WellDone/MoMo-Firmware/pcb/calculations/spice/controller/current_limiter.asc

D1: schottky; 1N5817
D2: schottky; 1N5817
M1: pmos; irlml6402
Q1: pnp
R1: res; 1
R2: res; 10k
R3: res; 100k
V1: voltage; 4.0
V3: voltage; PULSE(0 4.75 1 0.01 0.01 2)
V4: voltage; PULSE(0 3.8 0.5 0.01 0.01 2)
Named nets: 0
.tran 2
.lib irlml6402.spi
