WellDone/MoMo-Firmware/pcb/calculations/spice/controller/reset_circuit.asc

C1: cap; 1µ
C2: cap; 1µ
M1: nmos; 2N7002P
R1: res; 100k
R2: res; 100K
R3: res; 510K
R4: res; 10K
V1: voltage; PULSE(0 2.8 0.02 1e-6 1e-6 119e-3 2)
V2: voltage; 4.2
Named nets: V_enable, 0, discharge
.lib 2N7002P_8_18_2010.lib
.tran 0.5
Hardware Reset Generation
MoMo Controller v4.1
November 23, 2014
This circuit should reliably generate a
~100 ms low going pulse on V_enable
that must remain below 0.6V for > 50ms,
even without continued high input.
