WellDone/MoMo-Firmware/momo_modules/multi_sensor_module/src/state.h

#ifndef __state_h__
#define __state_h__

#include <stdint.h>

typedef struct
{
	union
	{
		struct
		{
			uint8_t acquire_pulse : 1;
			uint8_t push_pending : 1;
			uint8_t push_disabled: 1;
			uint8_t reserved : 5;
		};

		uint8_t combined_state;
	};
} MultiSensorState;

#endif
