WellDone/MoMo-Firmware/momo_modules/pic12_executive/src/bus_defines.h

#ifndef __bus_defines_h__
#define __bus_defines_h__

//Offsets from mib_data to the three overlapping buffers that store
//the command packet, return status and return value.
#define kCommandOffset 0
#define kReturnStatusOffset 1
#define kReturnValueOffset 3

//Bus error codes that can be returned
#define kNoMIBError 				0
#define kUnsupportedCommand 		1
#define kWrongParameterType 		2
#define kParameterTooLong 			3
#define kChecksumError				4
#define kUnknownError 				6
#define kCallbackError 				7
#define kSlaveNotAvailable 			255

//Other Constants
#define kInvalidMIBIndex			255
#define kBusMaxMessageSize 			20

#endif
