WellDone/MoMo-Firmware/momo_modules/mainboard/src/momo/report_manager.c

#include "report_manager.h"
#include "scheduler.h"
#include "momo_config.h"
#include "sensor_event_log.h"
#include "report_comm_stream.h"
#include "utilities.h"
#include "uart.h"
#include "base64.h"
#include "bus_master.h"
#include "perf.h"
#include "system_log.h"
#include "report_log.h"
#include "log_definitions.h"
#include <stdlib.h>
#include <string.h>

#define EVENT_BUFFER_SIZE         1

#define CONFIG current_momo_state.report_config

//Report structure, 118 bytes total
typedef struct 
{ 
    //18 byte header
    uint8          report_version;         // = 3, must be positive
    uint8          transmit_sequence;      //   How many times have we tried to transmit a report
    uint32         momo_uuid;              //   The unique ID of this MoMo
    uint16         flags;                  //   Various flags determining how the data will be aggregated and other things

    uint32         timestamp;
    uint16         battery_voltage;        //2

    uint8          bulk_aggregates;        //  The aggregate functions to run on the entire span
    uint8          interval_aggregates;    //  The aggregate functions to run on each interval

    union
    {
      struct
      {
      uint8        interval_type:4;        //  0: second, 1: minute, 2: hour, 3: day
      uint8        interval_step:4;        //
      };

      uint8        interval_union;
    };

    uint8          interval_count;         //  Up to 256 'intervals' each aggregated individually
    
    // 100 bytes for data (50 two byte report values)
    uint16         data[NUM_BUCKETS];
} Report;

typedef struct 
{
  uint16 count;
  uint16 min;
  uint16 max;
  uint16 sum;
} agg_counters;

static Report         report;
static ScheduledTask  report_task;
char                  base64_report_buffer[BASE64_REPORT_MAX_LENGTH+1];
static sensor_event   event_buffer[EVENT_BUFFER_SIZE];

//TODO: Implement dynamic report routing based on an initial "registration" ping to the coordinator address
#define DEFAULT_WEB_ROUTE "https://strato.welldone.org/gateway/http"
#define DEFAULT_SMS_ROUTE "+14159928370"
// UK ALT +447903568420
#define DEFAULT_GPRS_APN "JTM2M"

extern unsigned int last_battery_voltage;

void report_manager_start()
{
  if ( get_momo_state_flag( kStateFlagReportingEnabled ) )
    start_report_scheduling();
}

void init_report_config()
{
  strcpy( CONFIG.route_primary, DEFAULT_WEB_ROUTE );
  strcpy( CONFIG.route_secondary, DEFAULT_SMS_ROUTE );
  strcpy( CONFIG.gprs_apn, DEFAULT_GPRS_APN );
  CONFIG.transmit_sequence         = 0;
  CONFIG.report_interval           = kEveryDay;
  CONFIG.report_flags              = kReportFlagDefault;
  CONFIG.bulk_aggregates           = kAggMin | kAggMax;
  CONFIG.interval_aggregates       = kAggCount | kAggMean;
  CONFIG.retry_limit               = 3;

  //Make sure we initialize this scheduled task.
  report_task.flags = 0;

  init_comm_stream();
}

void update_interval_headers( Report* header, AlarmRepeatTime interval )
{
  switch ( interval )
  {
    case kEvery10Seconds:
      header->interval_union = pack_report_interval(kReportIntervalSecond, 1);
      header->interval_count = 10;
      break;
    case kEveryMinute:
      header->interval_union = pack_report_interval(kReportIntervalSecond, 6);
      header->interval_count = 10;
      break;
    case kEvery10Minutes:
      header->interval_union = pack_report_interval(kReportIntervalMinute, 1);
      header->interval_count = 10;
      break;
    case kEveryHour:
      header->interval_union = pack_report_interval(kReportIntervalMinute, 6);
      header->interval_count = 10;
      break;
    case kEveryDay:
    default:
      header->interval_union = pack_report_interval(kReportIntervalHour, 1);
      header->interval_count = 24;
      break;
  }
}

uint32 create_time_delta( const Report* header )
{
  //FIXME: is 0 a valid option for the caller of this function?
  switch ( header->interval_type )
  {
    case kReportIntervalSecond:
      return header->interval_step * header->interval_count;
    case kReportIntervalMinute:
      return 60 * header->interval_step * header->interval_count;
    case kReportIntervalHour:
      return 3600L * header->interval_step * header->interval_count;
  }
  return 0;
}

//Set bit counting routine from
//https://graphics.stanford.edu/~seander/bithacks.html
static uint8 agg_size(uint8 agg_set)
{
  uint8 size;

  for (size=0; agg_set; ++size)
    agg_set &= agg_set-1;

  return size;
}

static void init_agg( agg_counters* agg )
{
  agg->count = 0;
  agg->min = MAX_UINT16;
  agg->max = 0;
  agg->sum = 0;
}
static void update_agg( agg_counters* agg, sensor_event* event )
{
  ++(agg->count);
  agg->sum += event->value;
  if ( event->value < agg->min )
    agg->min = event->value;
  if ( event->value > agg->max )
    agg->max = event->value;
}
static uint8 finish_agg( agg_counters* agg, uint8 agg_set, uint8 index)
{
  if ( agg_set & kAggCount )
    report.data[index++] = agg->count;
  if ( agg_set & kAggSum )
    report.data[index++] = agg->sum;
  if ( agg_set & kAggMean )
    report.data[index++] = (agg->count==0)? 0 : agg->sum / agg->count;
  if ( agg_set & kAggMin )
    report.data[index++] = agg->min;
  if ( agg_set & kAggMax )
    report.data[index++] = agg->max;

  return index;
}

bool construct_report()
{
  PROFILE_START(kConstructReport);
  agg_counters    bulk_agg;
  agg_counters    int_agg;
  uint8           i, c;
  uint8           sensor_id = 0, curr_interval = 0;
  uint8           interval_bucket = agg_size(CONFIG.bulk_aggregates);
  uint8           max_bucket = NUM_BUCKETS - agg_size(CONFIG.interval_aggregates);

  //Initialize the report header
  report.report_version = MOMO_REPORT_VERSION;
  report.transmit_sequence = CONFIG.transmit_sequence;
  report.momo_uuid = current_momo_state.uuid;
  report.flags = CONFIG.report_flags;
  report.battery_voltage = last_battery_voltage;
  report.timestamp = rtcc_get_timestamp();
  report.bulk_aggregates = CONFIG.bulk_aggregates;
  report.interval_aggregates = CONFIG.interval_aggregates;

  update_interval_headers(&report, CONFIG.report_interval);

  uint32 time_delta = create_time_delta(&report);
  uint32 time_step = time_delta / report.interval_count;

  init_agg(&bulk_agg);
  init_agg(&int_agg);

  //Zero out the report structure
  for (i=0; i<NUM_BUCKETS; ++i)
    report.data[i] = 0;

  do
  {
    PROFILE_START(kProcessEventCounter);
    c = read_sensor_events( event_buffer, EVENT_BUFFER_SIZE );
    for ( i = 0; i < c; ++i )
    {
      if ( sensor_id == 0 )
        sensor_id = event_buffer[i].module;
      else if ( sensor_id != event_buffer[i].module )
        continue; // TODO: Support multiple sensor streams

      if (CONFIG.bulk_aggregates != kAggNone)
        update_agg( &bulk_agg, &event_buffer[i] );

      if (CONFIG.interval_aggregates != kAggNone)
      {
        uint32 time_seconds;
        uint8  event_interval;
        TimeIntervalDirection delta;

        if (interval_bucket >= max_bucket)
          continue; //TODO: Extend to a second SMS

        //Check if the event is too old and drop it
        //TODO: extend the report start backwards to pick up the dropped events?
        time_seconds = rtcc_timestamp_difference(event_buffer[i].timestamp, report.timestamp, &delta);
        if (time_seconds >= time_delta)
          continue;

        //Check if this event is somehow in the future
        if (delta == kNegativeDelta)
        {
          requeue_sensor_events( c - i );
          c = 0;
          break;
        }

        event_interval = report.interval_count - time_seconds/time_step - 1; //time_seconds/time_step < report.interval_count since time_seconds < time_delta

        //Check if this event corresponds to a new interval, in which case zero out the intervening
        //intervals.
        while (curr_interval < event_interval)
        {
          interval_bucket = finish_agg(&int_agg, CONFIG.interval_aggregates, interval_bucket);
          init_agg(&int_agg);

          ++curr_interval;
        }

        update_agg(&int_agg, &event_buffer[i]);
      }
    }
    PROFILE_END(kProcessEventCounter);
  }
  while (c > 0);

  //Finish the last interval
  if (CONFIG.interval_aggregates != kAggNone && interval_bucket < max_bucket)
    interval_bucket = finish_agg(&int_agg, CONFIG.interval_aggregates, interval_bucket);

  if ( CONFIG.bulk_aggregates != kAggNone)
    finish_agg(&bulk_agg, CONFIG.bulk_aggregates, 0);

  PROFILE_START(kEncodeReportCounter);
  i = base64_encode((const BYTE*)&report, RAW_REPORT_MAX_LENGTH, base64_report_buffer, BASE64_REPORT_MAX_LENGTH);
  PROFILE_END(kEncodeReportCounter);
  base64_report_buffer[i] = '\0';

  report_log_write( (BYTE*)&report );
  save_momo_state();
  
  PROFILE_END(kConstructReport);
  return true;
}

void post_report( void* arg ) 
{
  report_stream_abandon();
  LOG_DEBUG(kConstructingReportNotice);
  if (!construct_report( CONFIG.report_interval ))
  {
    LOG_CRITICAL(kFailedToConstructReportError);
    return; //TODO: Recover
  }

  LOG_DEBUG(kReportConstructedNotice);
  report_stream_send( base64_report_buffer );
}

void start_report_scheduling() {
  LOG_DEBUG(kReportSchedulingStartedNotice);
  scheduler_schedule_task( post_report, CONFIG.report_interval, kScheduleForever, &report_task, NULL );
}
void stop_report_scheduling() {
  LOG_DEBUG(kReportSchedulingStoppedNotice);
  scheduler_remove_task( &report_task );
}
void set_report_scheduling_interval( AlarmRepeatTime interval ) {
  if ( interval >= kNumAlarmTimes )
    return;

  CONFIG.report_interval = interval;
  if ( BIT_TEST(report_task.flags, kBeingScheduledBit) )
    scheduler_schedule_task( post_report, CONFIG.report_interval, kScheduleForever, &report_task, NULL );
  
  save_momo_state();
}
void update_report_route( uint8 index, uint8 start, const char* route, uint8 len )
{
  if ( index > 1 || start+len >= ROUTE_MAX_LENGTH )
    return;

  char* target = (index == 0)? CONFIG.route_primary : CONFIG.route_secondary;
  memcpy( target+start, route, len );
  target[start+len] = '\0';
  save_momo_state();
}

void set_gprs_apn( const char* apn, uint8 len )
{
  if ( len + 1 > sizeof(CONFIG.gprs_apn) )
    return;

  memcpy( CONFIG.gprs_apn, apn, len );
  CONFIG.gprs_apn[len] = '\0';
  save_momo_state();
}

const char* get_report_route( uint8 index )
{
  if ( index > 1 )
    return NULL;
  return ( index == 0 ) ? CONFIG.route_primary : CONFIG.route_secondary;
}
