WellDone/MoMo-Firmware/momo_modules/shared/pic24/src/mib/rpc_queue.c

#include "rpc_queue.h"
#include "task_manager.h"
#include "system_log.h"

#ifndef __TEST__
#include "log_definitions.h"
#endif 

#include <string.h>

static rpc_info   the_rpc_queue_data[RPC_QUEUE_SIZE];
static ringbuffer the_rpc_queue;

void rpc_queue_init()
{
	ringbuffer_create( &the_rpc_queue, the_rpc_queue_data, sizeof(rpc_info), RPC_QUEUE_SIZE );
}

void rpc_queue(mib_rpc_function callback, const MIBUnified *data)
{
	uninterruptible_start();
	if ( rpc_queue_full() ) 
	{
		LOG_CRITICAL(kRPCQueueFullError);
		uninterruptible_end();
		return;  // THIS IS REALLY BAD!!!!!!
	}
	rpc_info info;
	info.callback = callback;
	memcpy(&info.data, data, sizeof(MIBUnified));

	ringbuffer_push(&the_rpc_queue, &info);

	if ( rpc_queue_full() )
		taskloop_lock();
	uninterruptible_end();
}

inline void rpc_dequeue(rpc_info* out)
{
	uninterruptible_start();
	ringbuffer_pop(&the_rpc_queue, out);
	taskloop_unlock();
	uninterruptible_end();
}
inline const rpc_info* rpc_queue_peek()
{
	return ringbuffer_peek( &the_rpc_queue);
}

inline bool rpc_queue_full()
{
	return ringbuffer_full( &the_rpc_queue );
}
inline bool rpc_queue_empty()
{
	return ringbuffer_empty( &the_rpc_queue );
}
