WellDone/MoMo-Firmware/momo_modules/shared/pic24/src/mib/rpc_queue.h

#ifndef __rpc_queue_h
#define __rpc_queue_h

#include "bus.h"

#include "ringbuffer.h"

#define RPC_QUEUE_SIZE 8 // Must be a power of 2

typedef struct {
	mib_rpc_function callback;
	MIBUnified 		 data;
} rpc_info;

void rpc_queue_init();
void rpc_queue( mib_rpc_function callback, const MIBUnified *data);
inline void rpc_dequeue(rpc_info* out);
inline const rpc_info* rpc_queue_peek();
inline bool rpc_queue_full();
inline bool rpc_queue_empty();

#endif
