WellDone/MoMo-Firmware/momo_modules/shared/pic24/src/mib/slave/bus_slave.h

#ifndef __bus_slave_h__
#define __bus_slave_h__

#include "bus.h"

//Slave Routines
void bus_slave_callback();
void bus_slave_return_int16( int16 val );
void bus_slave_return_buffer( const void* buff, uint8 length );
inline void bus_slave_set_returnbuffer_length( uint8 length );
void bus_slave_setreturn(uint8 status);

#endif
