WellDone/MoMo-Firmware/momo_modules/pic12_executive/src/bootloader.h

#ifndef __bootloader_h__
#define __bootloader_h__

#include "bootloader_defs.h"

#define kRetlwHighWord			0b110100

#define set_flash_word(offset, low, high) 	{app_buffer[offset << 1] = low; app_buffer[(offset << 1) + 1] = high;}

#ifndef _DEFINES_ONLY
#include "platform.h"
#include "flash_memory.h"

void 	set_firmware_id(uint8 bucket);
void 	prepare_reflash(uint8 source);
void 	enter_bootloader();
void 	get_half_row();

//1 Byte
typedef union
{
	struct
	{
		uint8 timer_running	: 1; //set when we receive an edge on ALARM so that we can check for 2 edges in one timeout period
		uint8 valid_app 	: 1;
		uint8 bootload_mode : 1;
		uint8 registered	: 1;
		uint8 dirty_reset 	: 1; //cannot change, referenced in watchdog.as
		uint8 slave_active 	: 1; //cannot change, referenced in i2c_utilities.as
		uint8 first_read	: 1;
		uint8 trapped		: 1; 
	};

	uint8 status;
} MIBExecutiveStatus;

#endif


#endif
